kanpapa/TangConsoleDCJ11MEM/hdl/20251017/TangConsoleDCJ11MEM_project/src/integer_division/integer_division_tmp.v

//Copyright (C)2014-2025 Gowin Semiconductor Corporation.
//All rights reserved.
//File Title: Template file for instantiation
//Tool Version: V1.9.11.02 (64-bit)
//Part Number: GW5AST-LV138PG484AC1/I0
//Device: GW5AST-138
//Device Version: B
//Created Time: Thu Aug 21 10:04:02 2025

//Change the instance name and port connections to the signal names
//--------Copy here to design--------

	Integer_Division_Top your_instance_name(
		.clk(clk), //input clk
		.rstn(rstn), //input rstn
		.dividend(dividend), //input [31:0] dividend
		.divisor(divisor), //input [15:0] divisor
		.remainder(remainder), //output [15:0] remainder
		.quotient(quotient) //output [31:0] quotient
	);

//--------Copy end-------------------
